Altay4Alp/FS_Corsa_General_PCB/Images/pcb_back.png

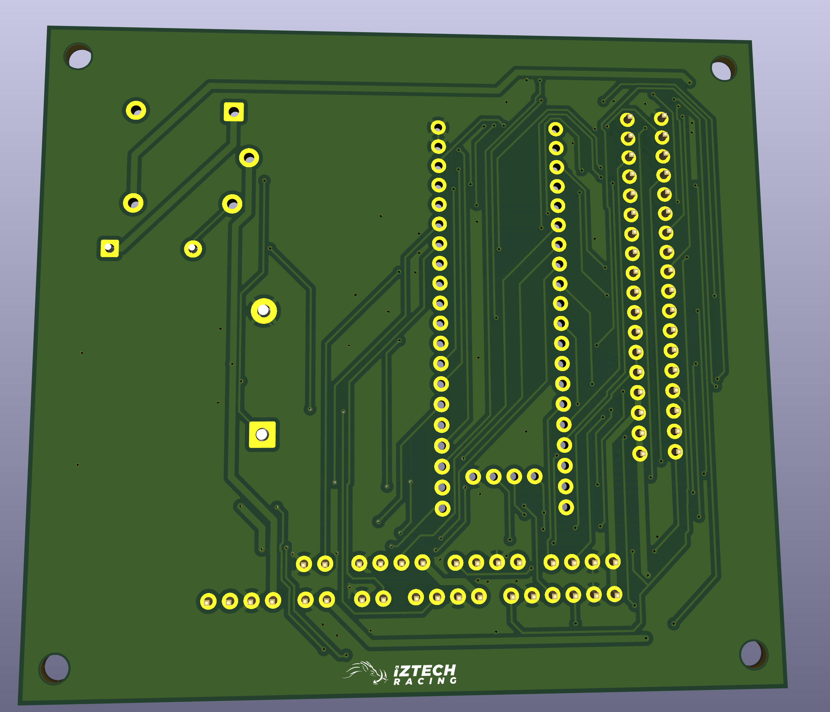
Images/pcb_back.png
