Altay4Alp/FS_Corsa_General_PCB/Images/Pwr_Sch.png

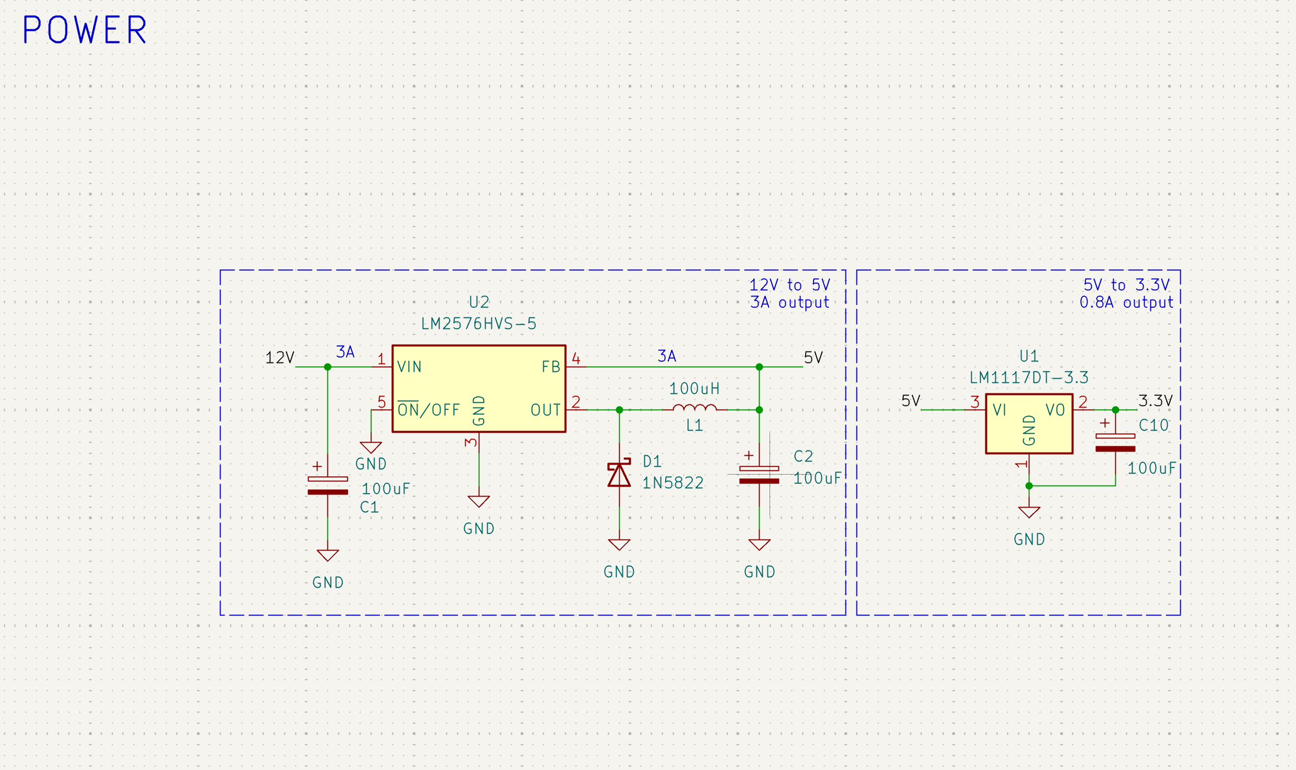
Images/Pwr_Sch.png
