Altay4Alp/FS_Corsa_General_PCB/Images/relay_sch.png

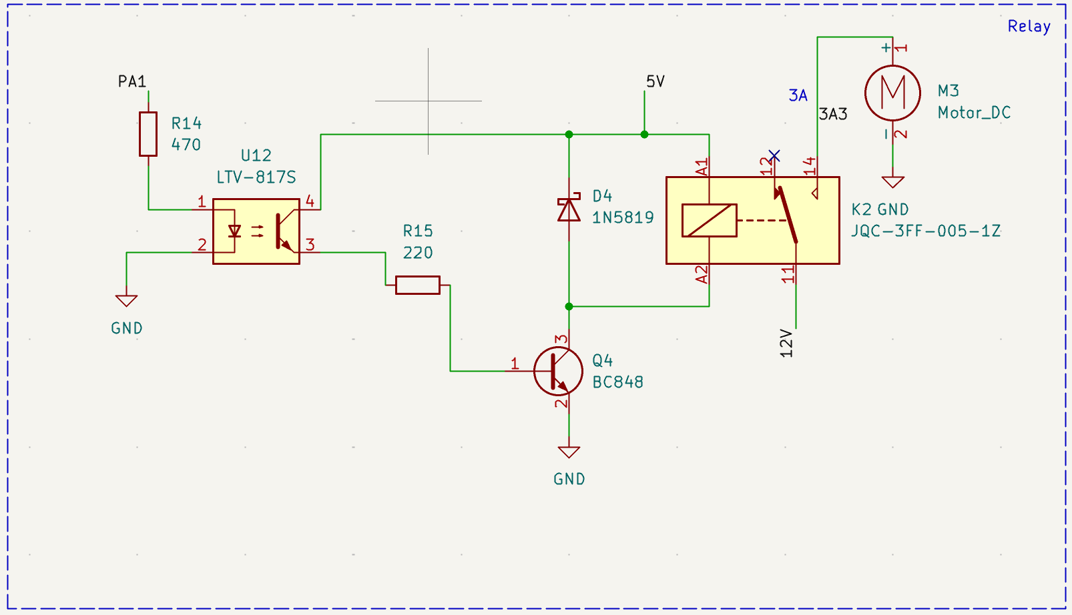
Images/relay_sch.png
