Altay4Alp/FS_Corsa_General_PCB/Images/stm32_sch.png

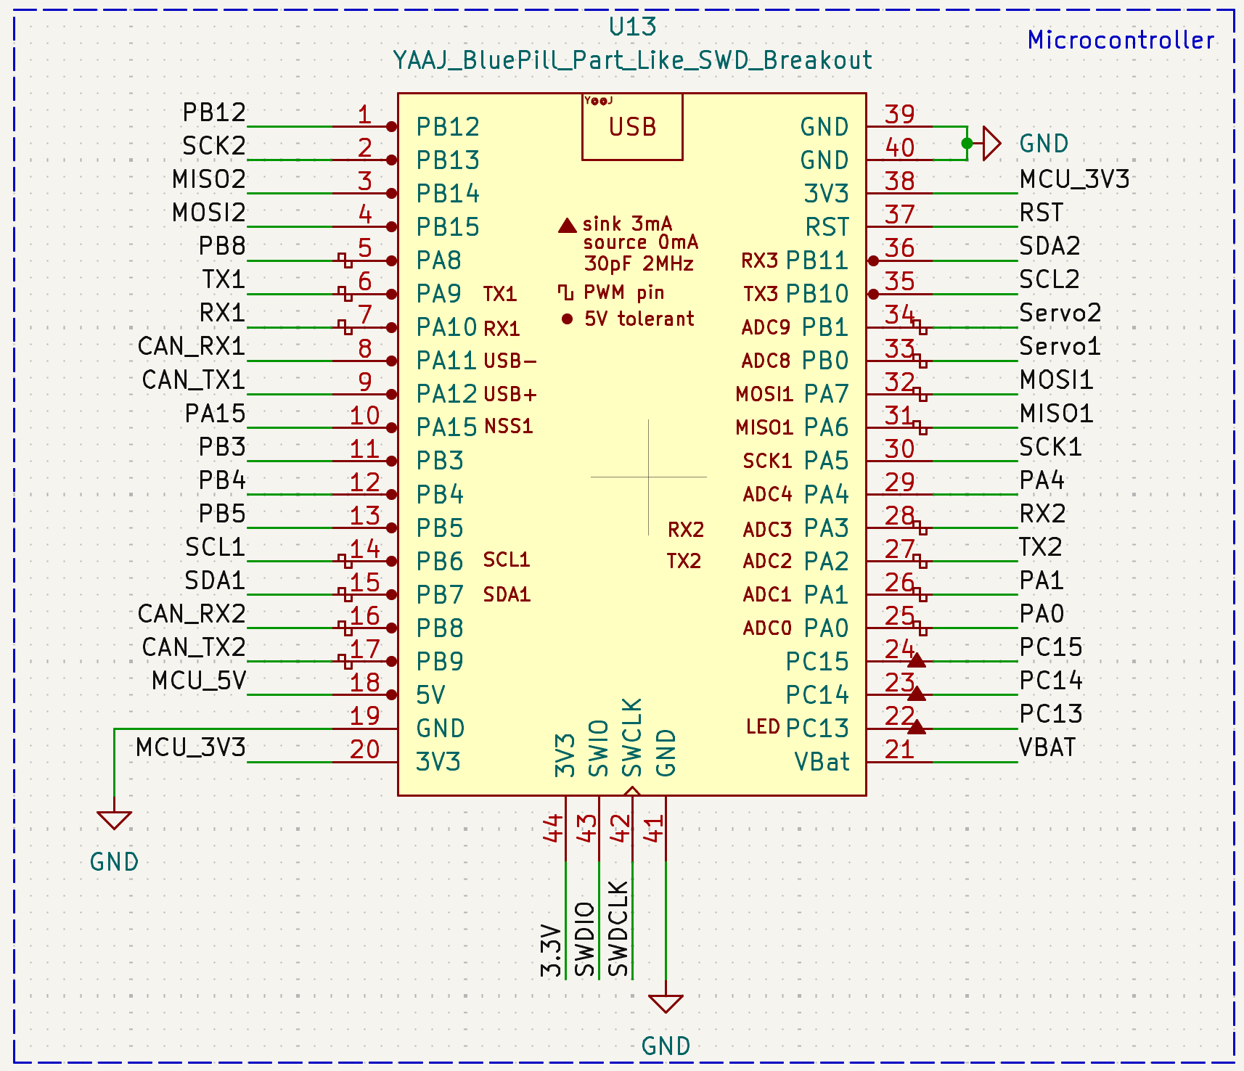
Images/stm32_sch.png
